manek11/Line-Following-Robot-Car/twitter.py

from twython import Twython

consumer_key = 'IbZYLMhINCxuxRLd4OyrM2Ph2'
consumer_secret = 'pBfsBvgDYBTjcXuYNgJXl5DhwXNEosZStpjCu4az7SgTvgyMcx'
access_token = '1220402110610604032-0Eca0tLBOjE2TKd1fPbh6BfZzMZ4u2'
access_token_secret = 'GH4fuU3riSkWVh0UGODAasDCI2gN8Qqpc7AkGlQnwzHQZ'

twitter = Twython(
    consumer_key,
    consumer_secret,
    access_token,
    access_token_secret
)

messages = [
    "Hello world",
    "Hi there",
    "What's up?",
    "How's it going?",
    "Have you been here before?",
    "Get a hair cut!",
]

# message = random.choice(messages)
# twitter.update_status(status=message)
# print("Tweeted: %s" % message)
# distance and angle are from sonar servo mount, state is to be defined as a string, imageFile contains
# the name of the photo taken by the camera in a .jpg/.png format
def postTweet(distance, angle, state, imageFile):
    if state == "end":
        message = "I have finished running the track!"
        if distance <= 10:
            message += "There is an object " + str(distance) + " cm away at " \
                       + str(angle) + " degrees from the right. We almost crashed!!"
        elif distance >= 100:
            message += "There are no obstacles in sight! The closest barrier is " \
                       + str(distance) + "cm away at " + str(angle) + " degrees from the right."
        image = open(imageFile, 'rb')
        response = twitter.upload_media(media=image)
        media_id = [response['media_id']]
        twitter.update_status(status=message, media_id=media_id)
        print("Tweeted: " + message)
